ChunkLightTuna/monitor_control/src/server.py

import gc
import json
import logging
import tracemalloc

import objgraph
from fastapi import HTTPException, Request, FastAPI, status, APIRouter
from fastapi.responses import FileResponse, HTMLResponse, Response

from lcd import Msg
from main_menu import MainMenu

# Start tracemalloc at app startup
tracemalloc.start()

router = APIRouter()

with open('res/index.html', 'r') as f:
    index = HTMLResponse(content=f.read())

favicon = FileResponse(path='res/favicon.ico', media_type="text/x-favicon")


@router.get("/favicon.ico")
async def get_favicon():
    return favicon


@router.get("/")
async def get_index():
    return index


@router.post("/")
async def post(request: Request):
    body = await request.body()

    try:
        line_one, line_two = json.loads(body.decode('utf-8'))
        if not line_one and not line_two:
            raise HTTPException(status_code=status.HTTP_400_BAD_REQUEST, detail="Both lines empty")
        elif len(line_one) > 16 or len(line_two) > 16:
            raise HTTPException(status_code=status.HTTP_400_BAD_REQUEST, detail="Max 16 char per line")
        else:
            message = Msg(line_one, line_two)
            menu: MainMenu | None = request.app.extra.get('menu')
            if menu:
                menu.msg_ephemeral(message)
            else:
                logging.info(message)

            return Response(status_code=status.HTTP_200_OK)
    except Exception as e:
        if 'not enough values to unpack' in repr(e):
            raise HTTPException(status_code=status.HTTP_400_BAD_REQUEST, detail="Ya gotta give me something")
        else:
            logging.error(repr(e))
            raise HTTPException(status_code=status.HTTP_500_INTERNAL_SERVER_ERROR)


@router.get("/debug/memory")
async def memory_debug():
    # Get current memory snapshot
    snapshot = tracemalloc.take_snapshot()
    top_stats = snapshot.statistics('lineno')

    # Get object counts
    types = objgraph.most_common_types(limit=20)

    # Force garbage collection and get counts
    gc.collect()

    return {
        "top_memory_allocations": [
            {
                "file": stat.traceback[0].filename,
                "line": stat.traceback[0].lineno,
                "size": stat.size,
                "count": stat.count
            }
            for stat in top_stats[:10]
        ],
        "object_counts": dict(types),
        "total_tracked_memory": tracemalloc.get_traced_memory()
    }

if __name__ == '__main__':
    import sys
    import uvicorn

    app = FastAPI()
    app.include_router(router)
    port = int(sys.argv[-1]) if len(sys.argv) > 1 else 8080
    uvicorn.run(app, host='0.0.0.0', port=port)
